ThumbsupCat/Inktime_TSC_Project/Images/Inside_case_no_lid.png

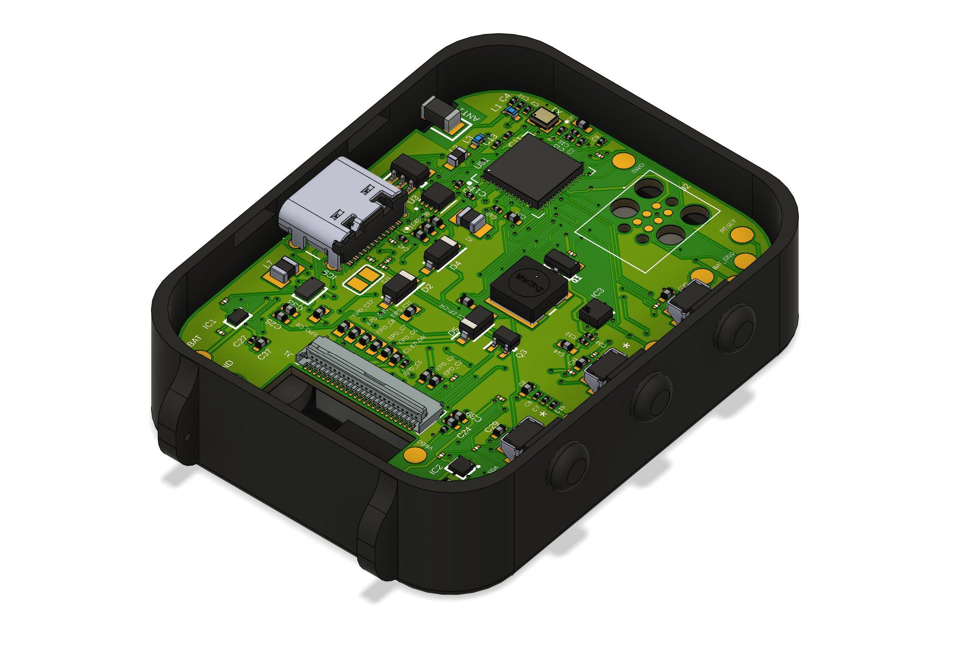
Images/Inside_case_no_lid.png
