ThumbsupCat/Inktime_TSC_Project/Images/PCB_size_view_mirror.png

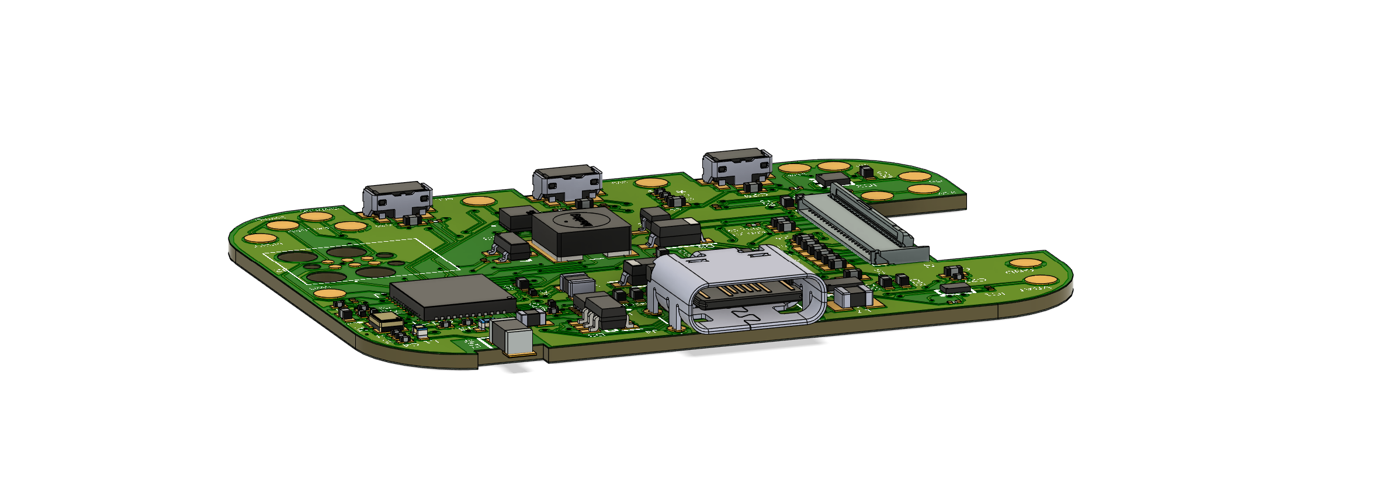
Images/PCB_size_view_mirror.png
