ThumbsupCat/Inktime_TSC_Project/Images/Components + display.png

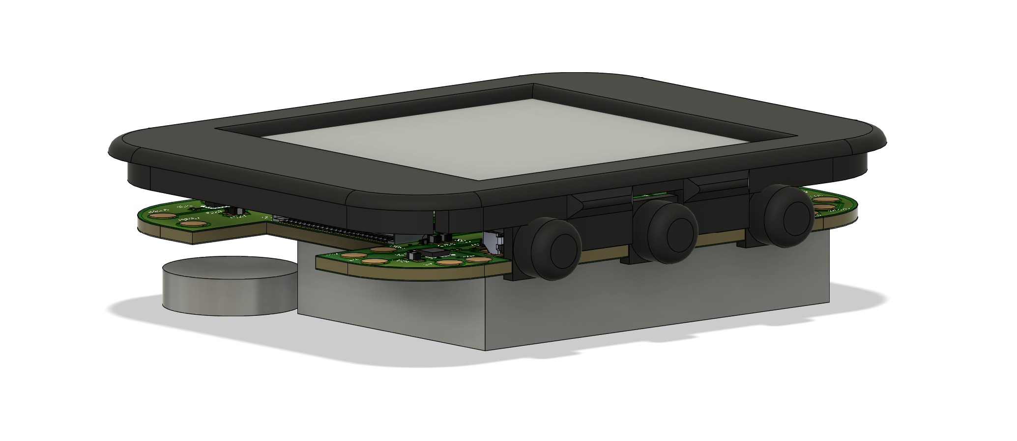
Images/Components + display.png
