ThumbsupCat/Inktime_TSC_Project/Images/Assembled_product_Buttons_angle.png

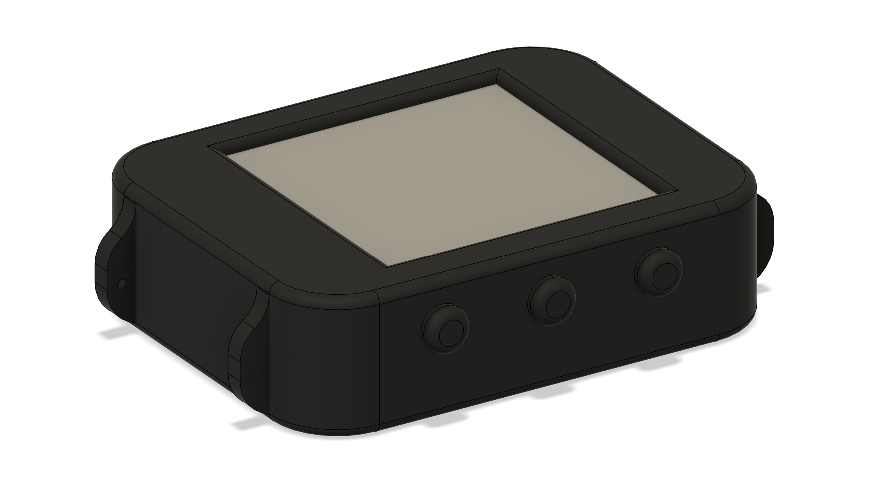
Images/Assembled_product_Buttons_angle.png
