ThumbsupCat/Inktime_TSC_Project/Images/Assembled_product_USB_angle.png

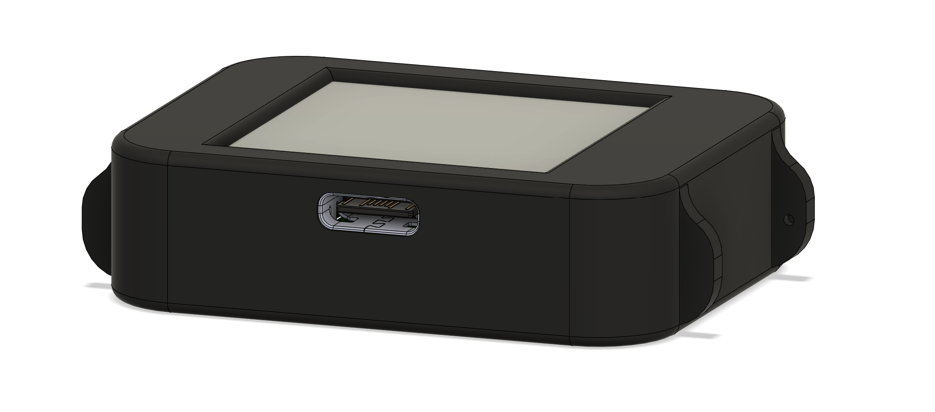
Images/Assembled_product_USB_angle.png
