ThumbsupCat/Inktime_TSC_Project/Images/assembly_exploded.png

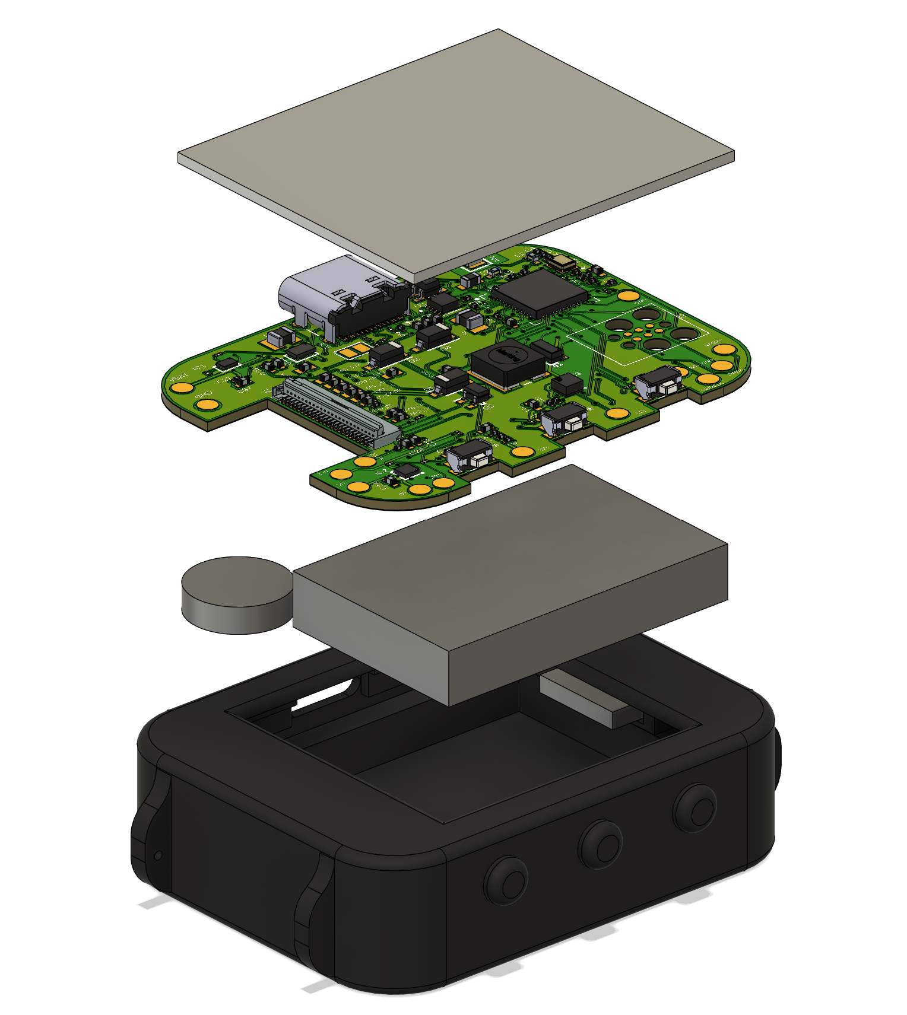
Images/assembly_exploded.png
