ThumbsupCat/Inktime_TSC_Project/Images/Assembly_exploded_mirror.png

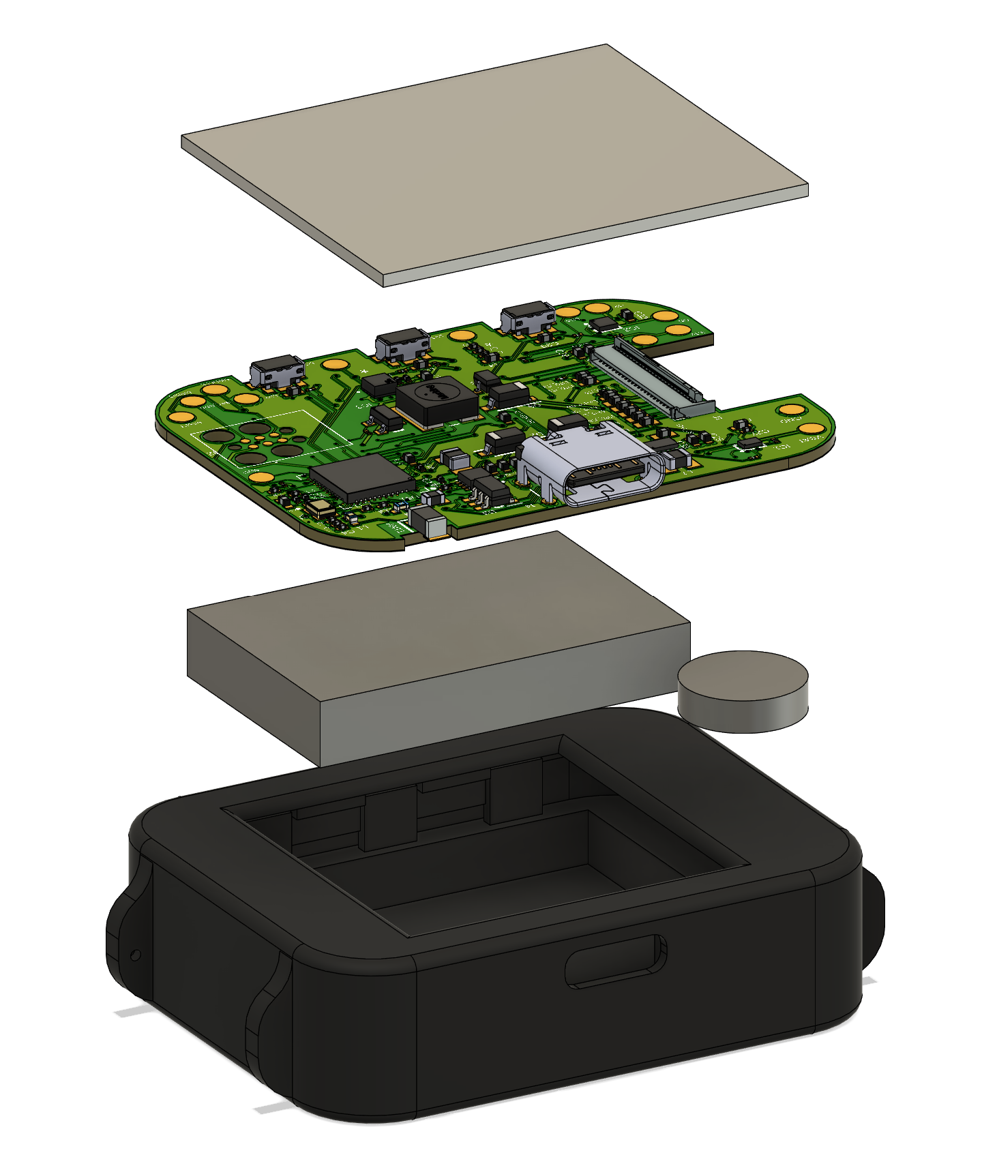
Images/Assembly_exploded_mirror.png
